andriymelnykov/Electronic_Eyepiece_for_CDK20/3D_Models/Eyepiece_Body_Layer0_1_RandomSeam.step

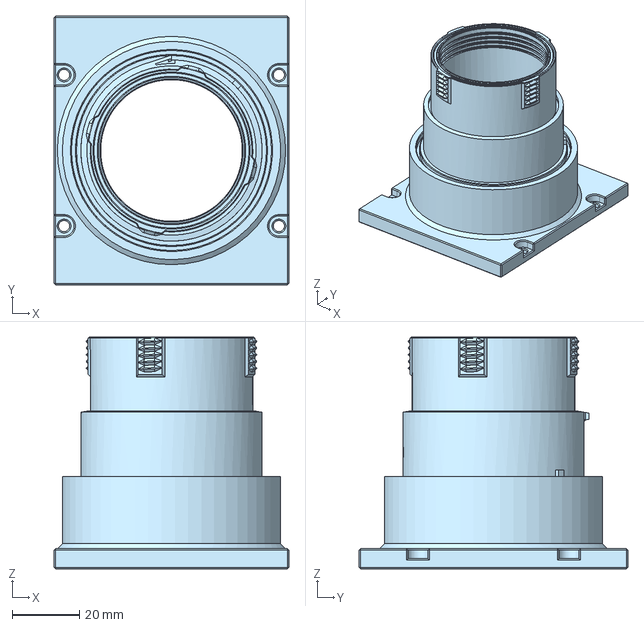
[picture p17: CAD file, 2026-09-20]
3D_Models/Eyepiece_Body_Layer0_1_RandomSeam.step
70.0 x 80.0 x 69.0 mm
