andriymelnykov/Electronic_Eyepiece_for_CDK20/3D_Models/Keyboard_Part1.step

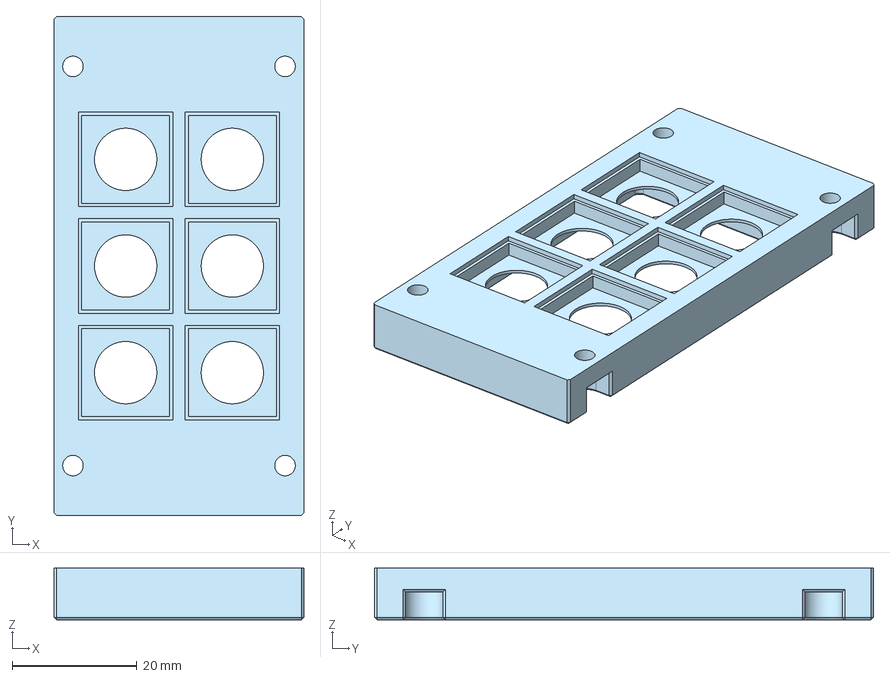
[picture p18: CAD file, 2026-09-20]
3D_Models/Keyboard_Part1.step
40.0 x 80.0 x 8.30 mm
