andriymelnykov/Electronic_Eyepiece_for_CDK20/3D_Models/Eyepiece_Cap_TPU.step

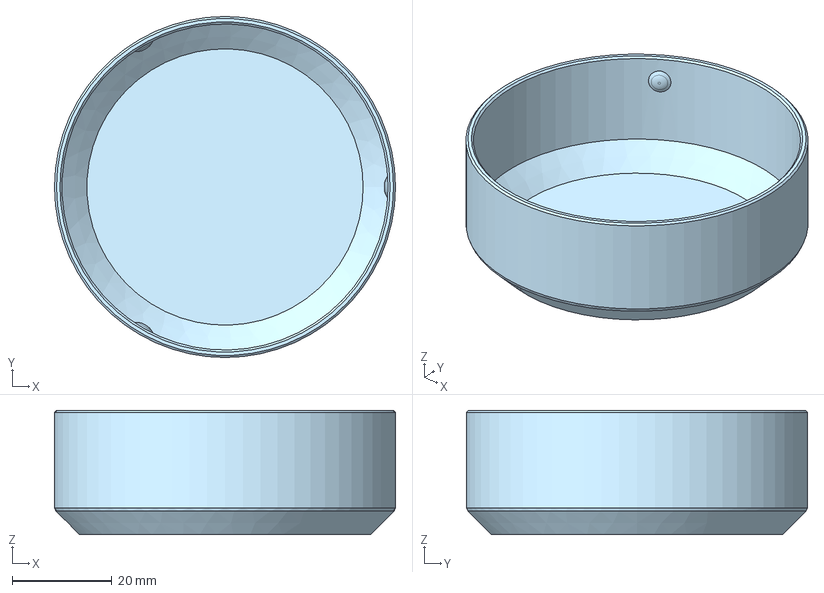
[picture p19: CAD file, 2026-09-20]
3D_Models/Eyepiece_Cap_TPU.step
68.5 x 68.5 x 25.0 mm
