andriymelnykov/Electronic_Eyepiece_for_CDK20/Assembly/11_Assembly.jpg

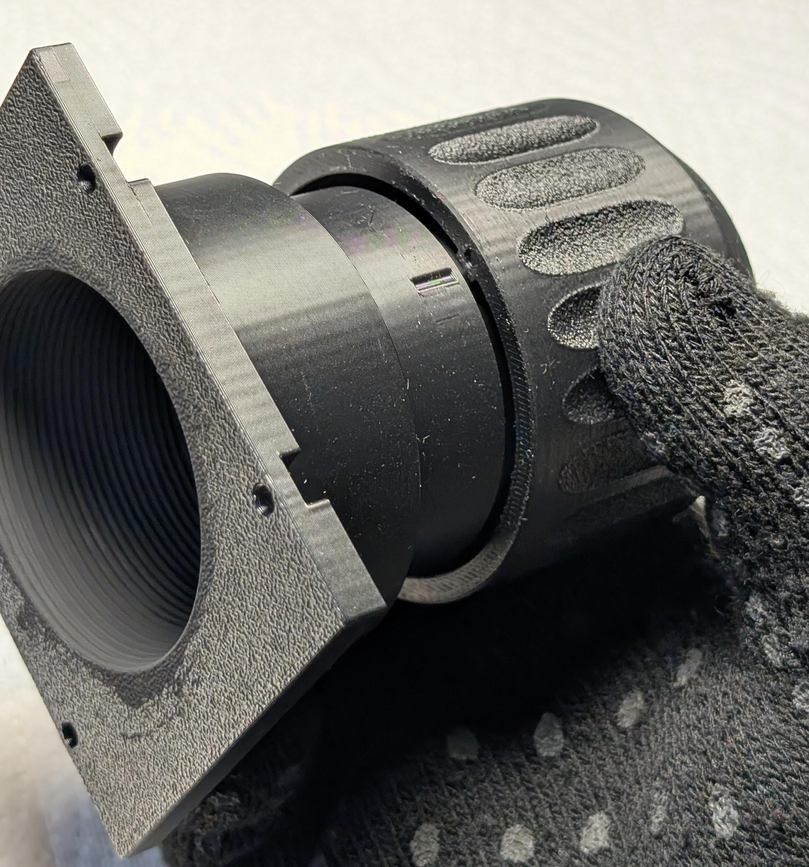
Assembly/11_Assembly.jpg
