andriymelnykov/Electronic_Eyepiece_for_CDK20/Assembly/12_Assembly.jpg

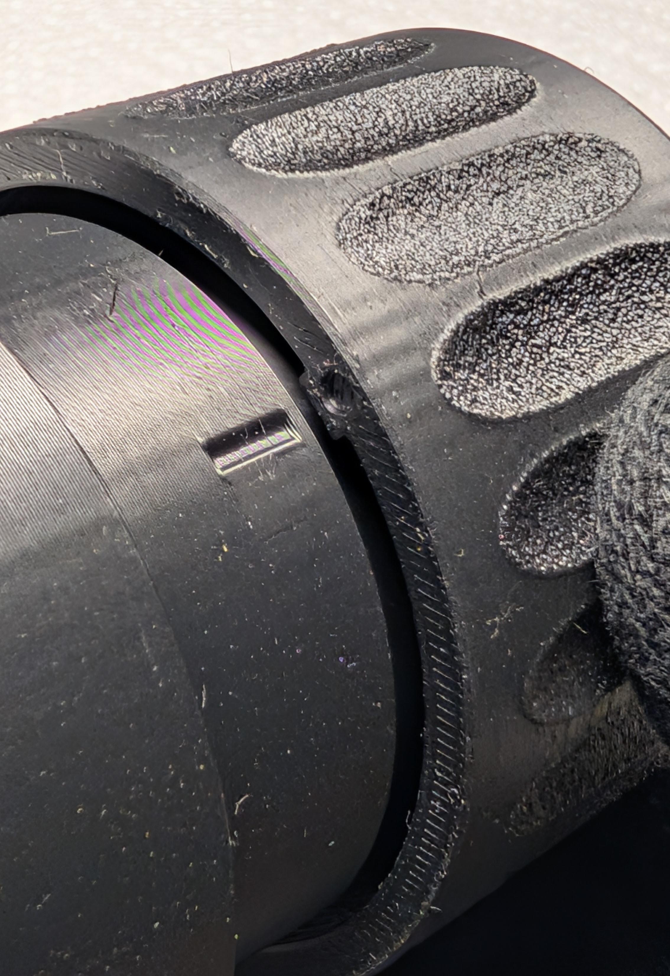
Assembly/12_Assembly.jpg
