andriymelnykov/Electronic_Eyepiece_for_CDK20/Assembly/16_Assembly.jpg

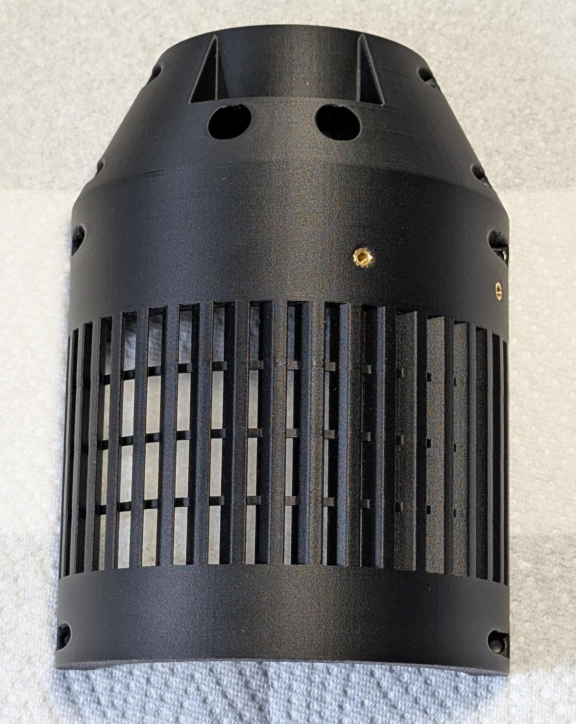
Assembly/16_Assembly.jpg
