andriymelnykov/Electronic_Eyepiece_for_CDK20/Assembly/22_Assembly.jpg

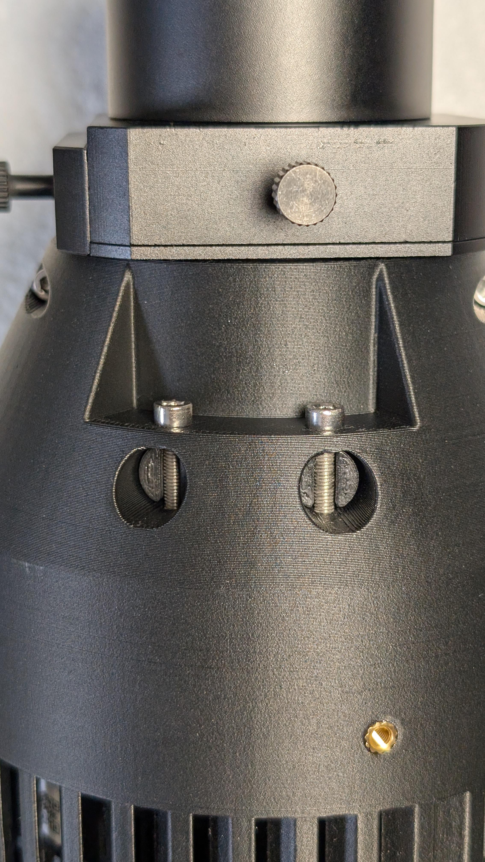
Assembly/22_Assembly.jpg
