andriymelnykov/Electronic_Eyepiece_for_CDK20/Assembly/27_Assembly.jpg

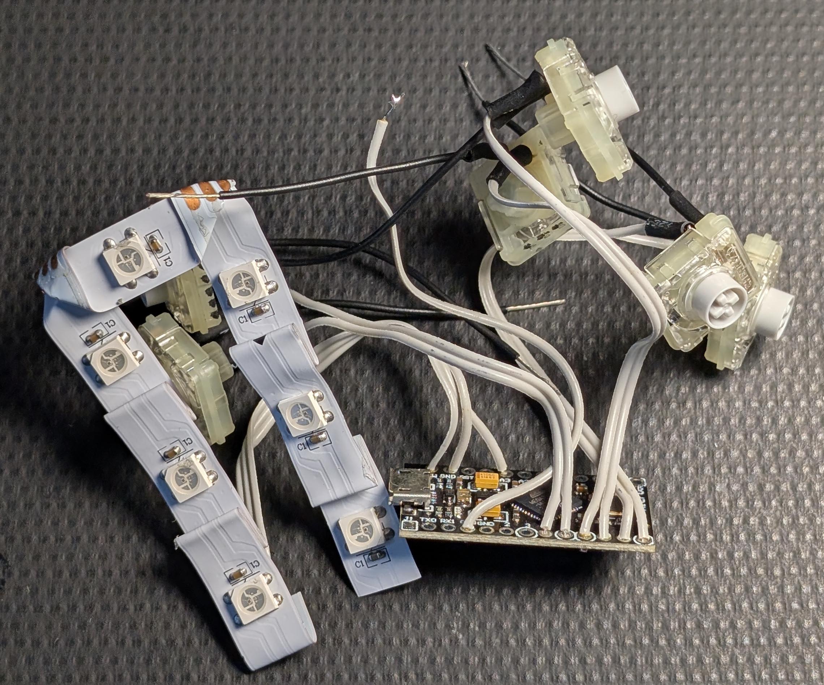
Assembly/27_Assembly.jpg
