andriymelnykov/Electronic_Eyepiece_for_CDK20/Assembly/28_Assembly.jpg

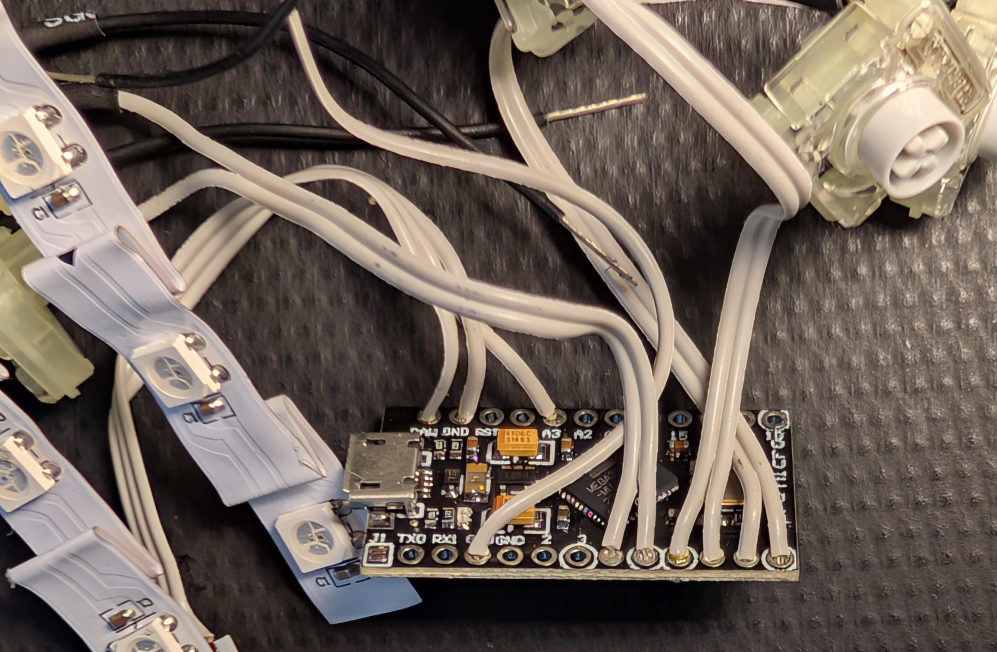
Assembly/28_Assembly.jpg
