andriymelnykov/Electronic_Eyepiece_for_CDK20/Assembly/30_Assembly.jpg

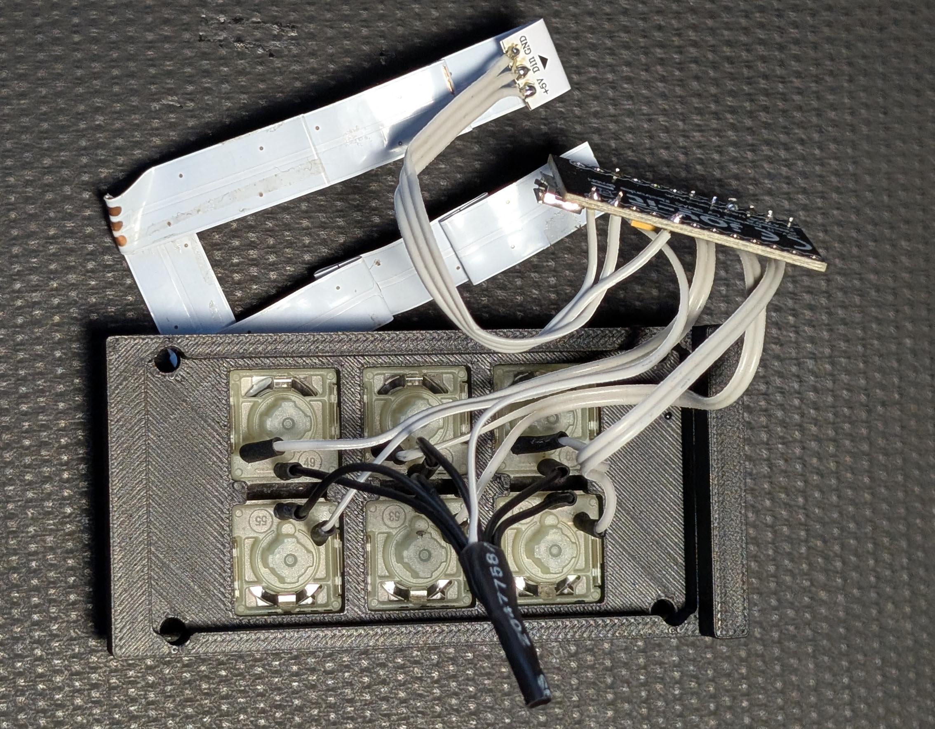
Assembly/30_Assembly.jpg
