andriymelnykov/Electronic_Eyepiece_for_CDK20/Assembly/31_Assembly.jpg

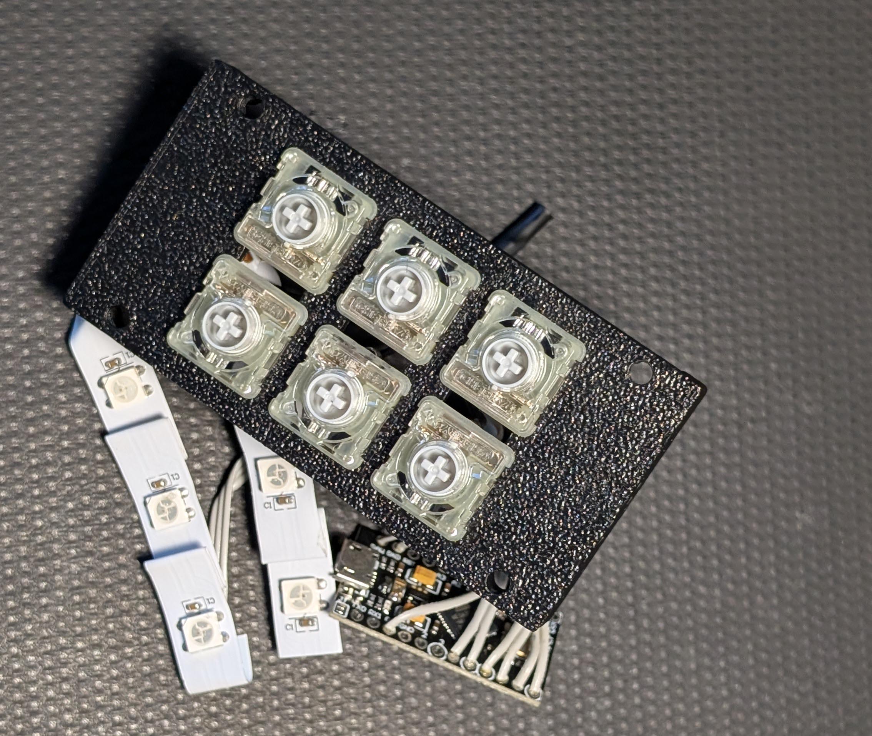
Assembly/31_Assembly.jpg
