andriymelnykov/Electronic_Eyepiece_for_CDK20/Assembly/32_Assembly.jpg

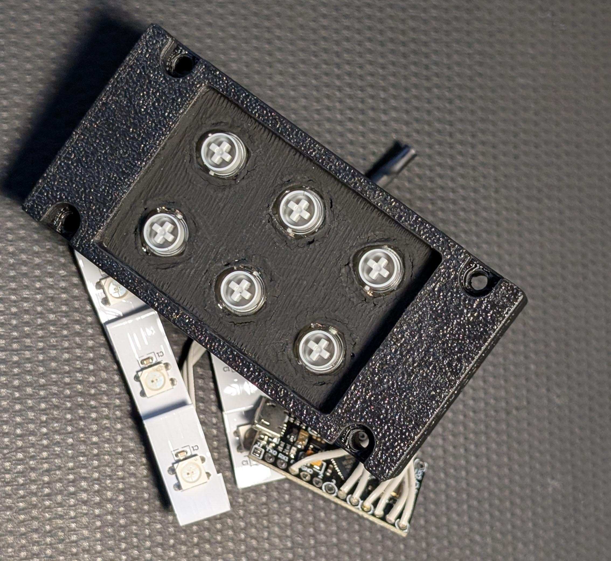
Assembly/32_Assembly.jpg
