andriymelnykov/Electronic_Eyepiece_for_CDK20/Assembly/33_Assembly.jpg

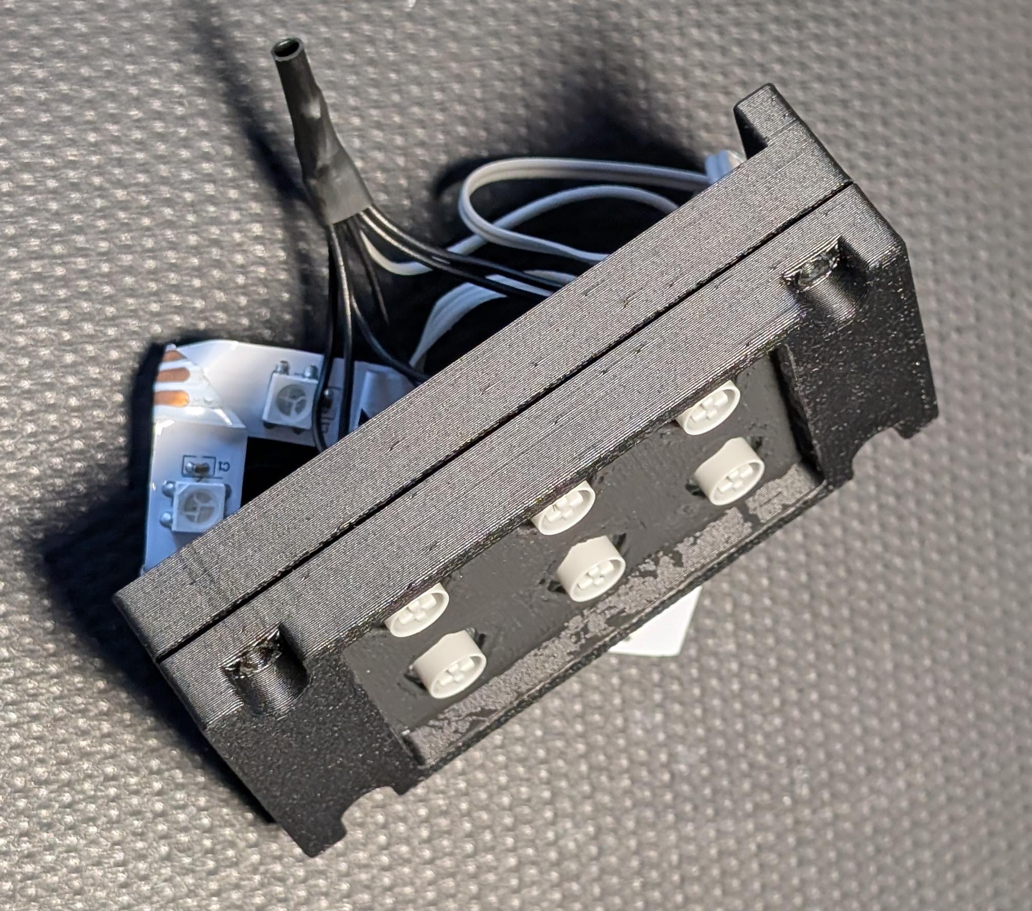
Assembly/33_Assembly.jpg
