andriymelnykov/Electronic_Eyepiece_for_CDK20/Assembly/38_Assembly.jpg

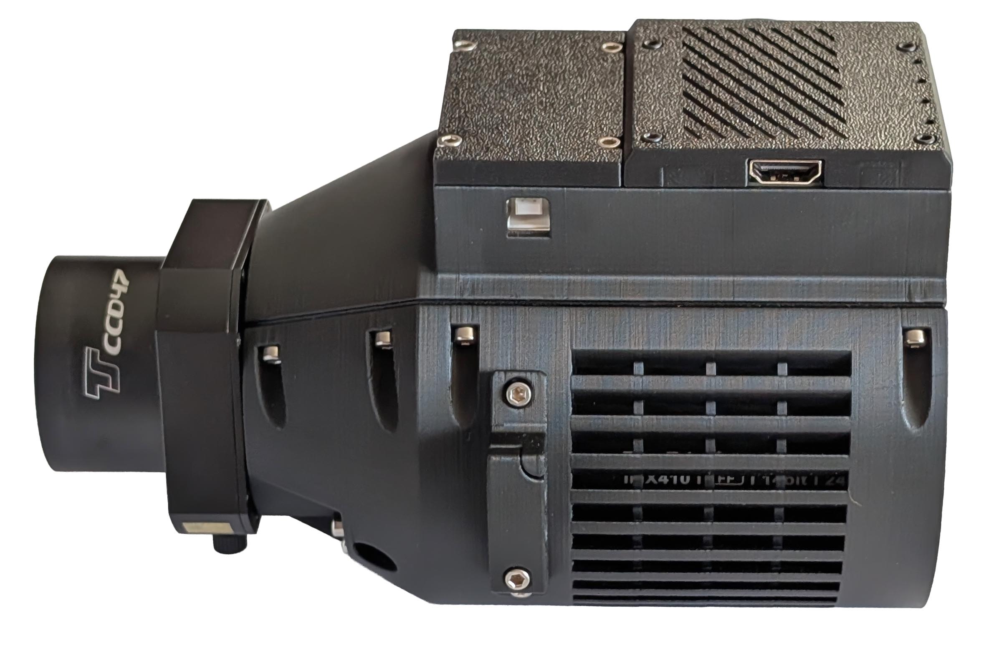
Assembly/38_Assembly.jpg
